flupes/digibaro2/brochure/digibaro_no-face.jpg

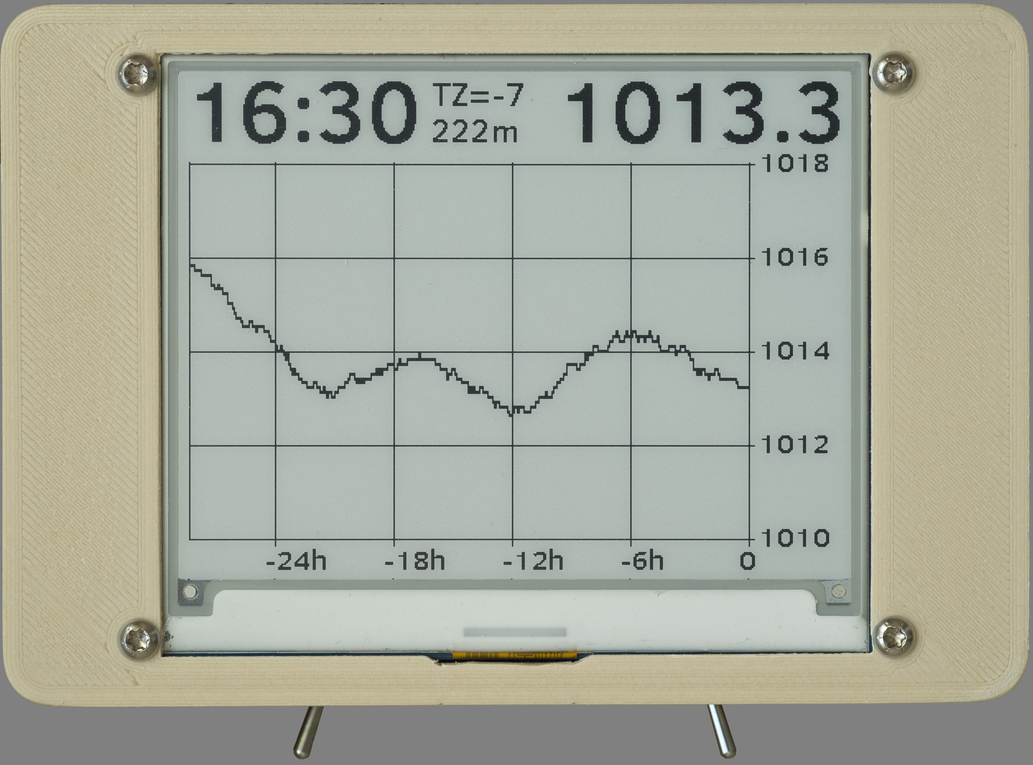
brochure/digibaro_no-face.jpg
