flupes/digibaro2/brochure/A_intro/1024px-Barograph_-_Image_from_page_45_of__Practical_physics__(1922).jpg

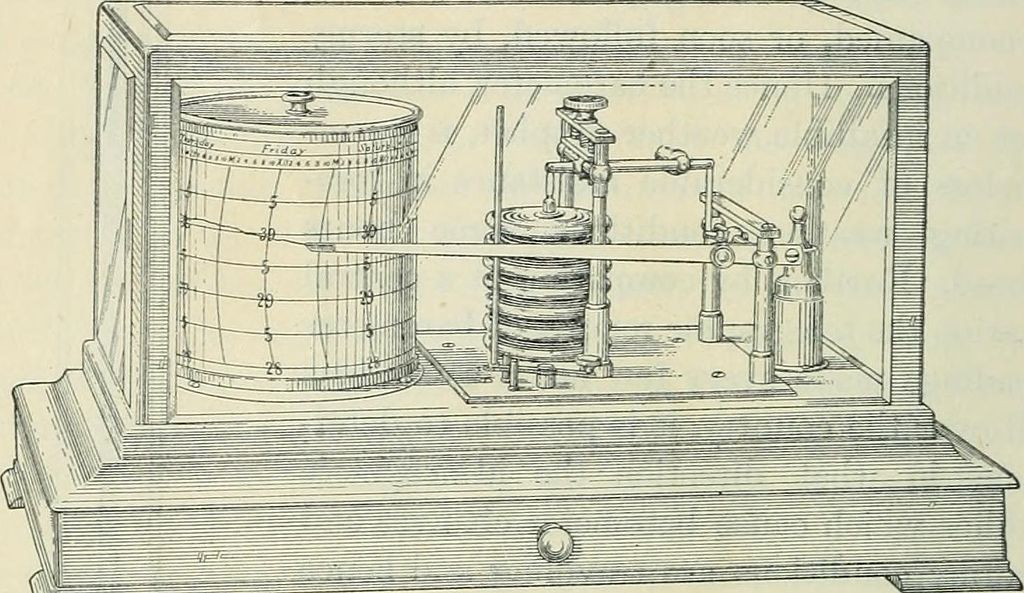
brochure/A_intro/1024px-Barograph_-_Image_from_page_45_of__Practical_physics__(1922).jpg
