flupes/digibaro2/brochure/A_intro/1926miamibarotrace.jpg

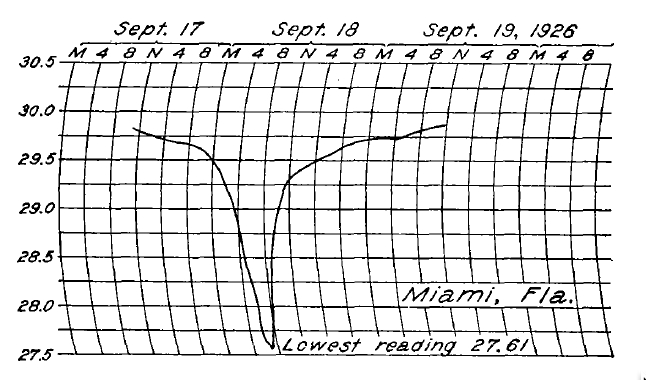
brochure/A_intro/1926miamibarotrace.jpg
