flupes/digibaro2/brochure/B_electro/B3_board-layout.png

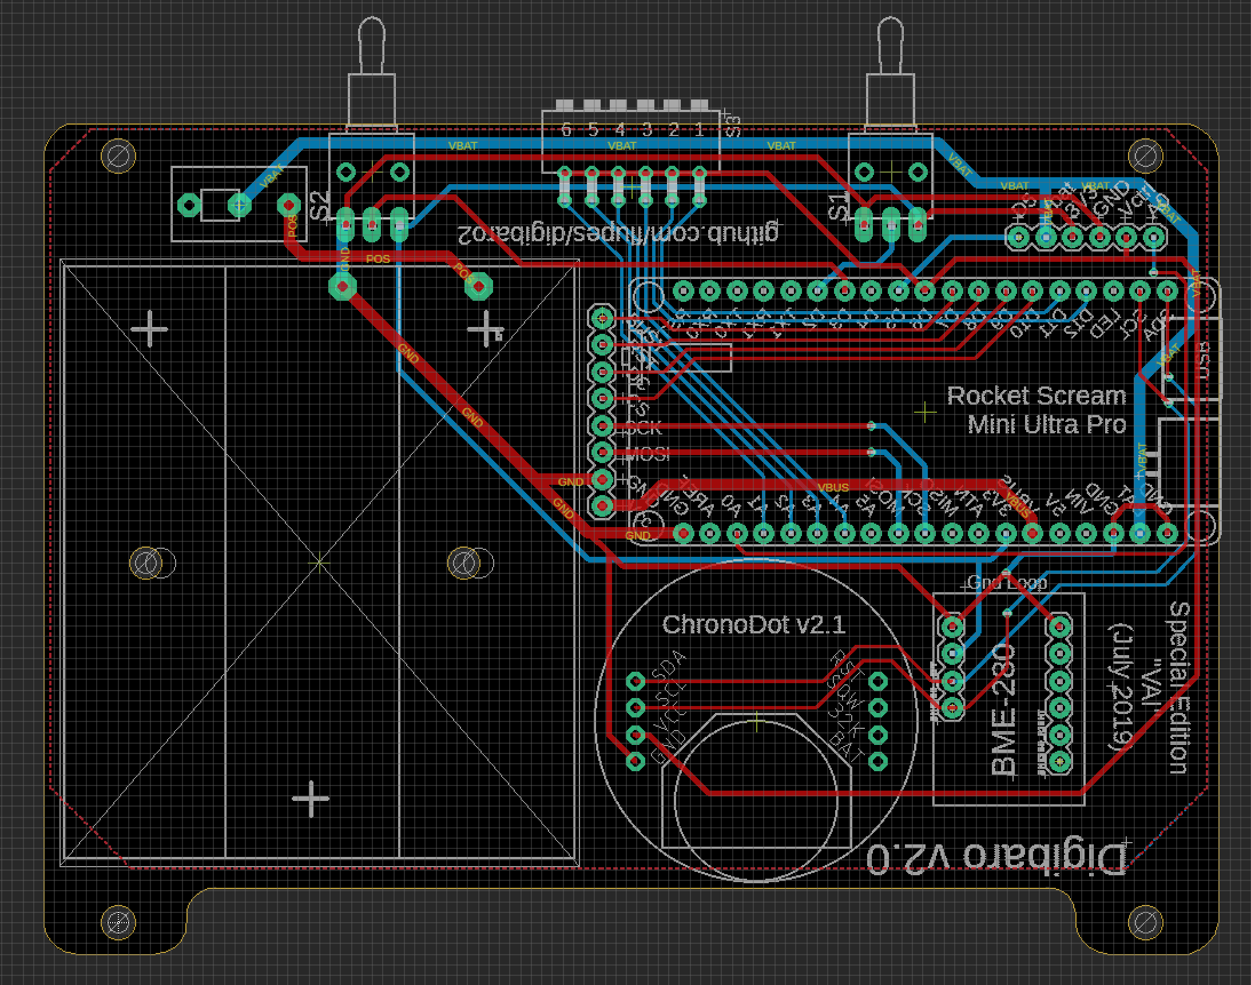
brochure/B_electro/B3_board-layout.png
