flupes/digibaro2/brochure/B_electro/B4_board-topring.png

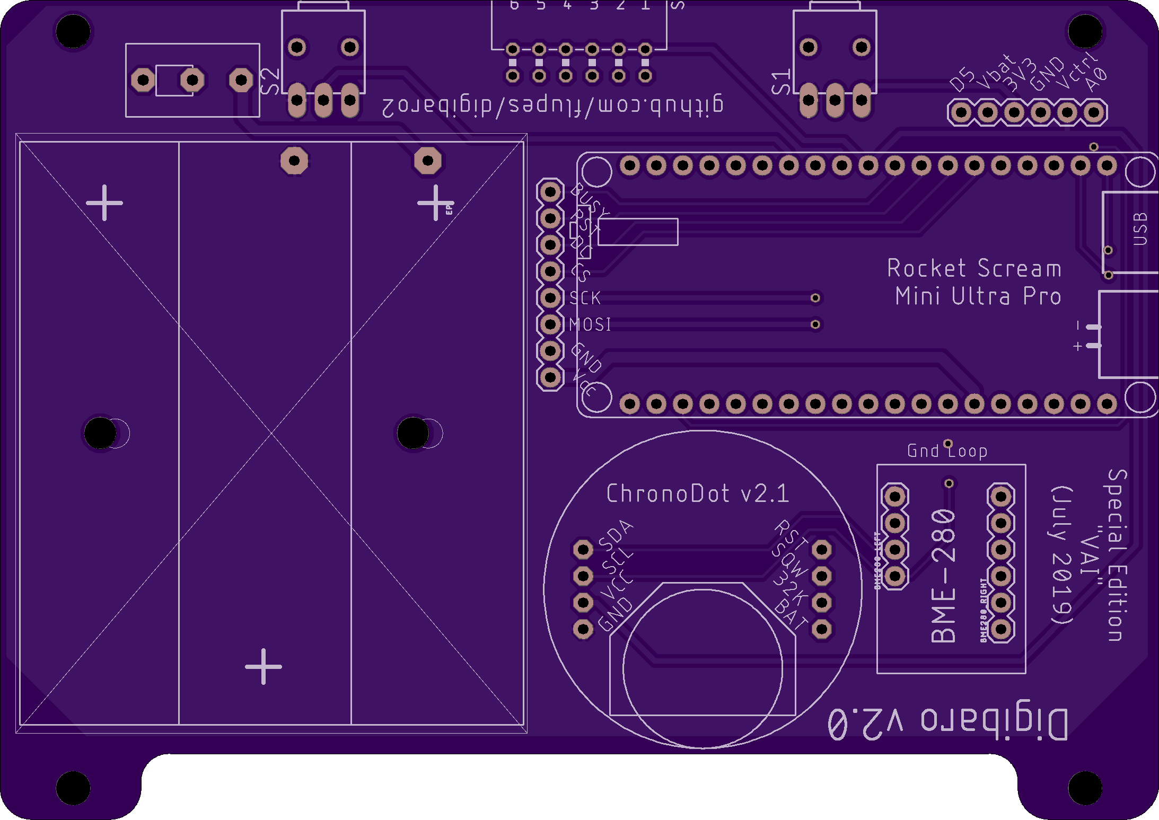
brochure/B_electro/B4_board-topring.png
