flupes/digibaro2/brochure/B_electro/B5_populated-board.jpg

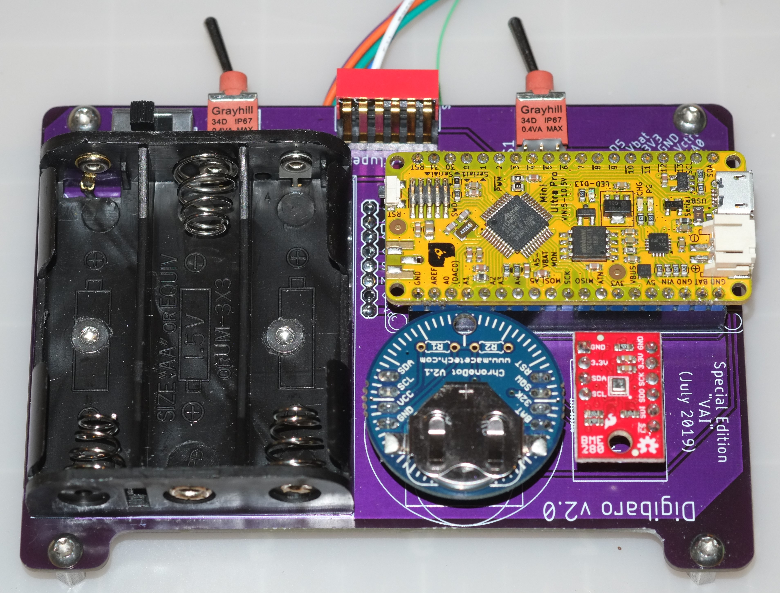
brochure/B_electro/B5_populated-board.jpg
