flupes/digibaro2/brochure/C_software/code.png

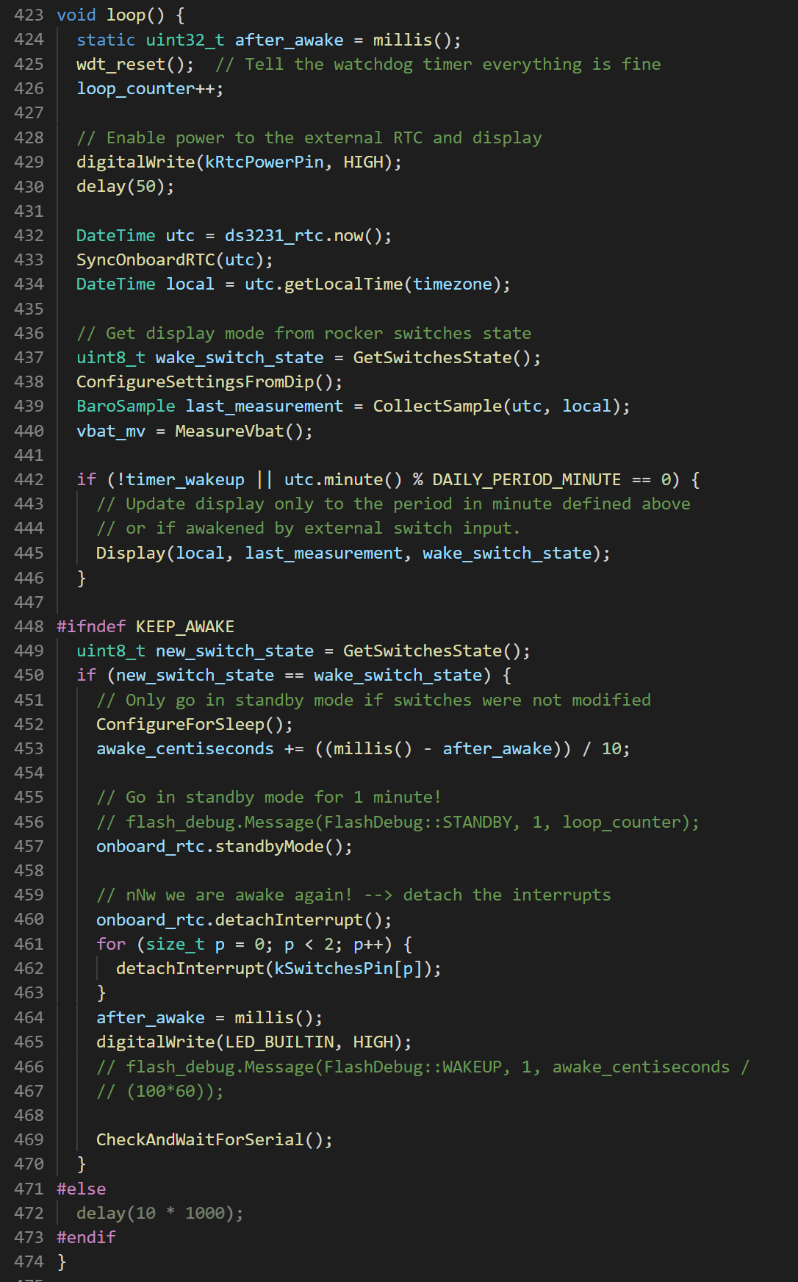
brochure/C_software/code.png
