flupes/digibaro2/brochure/digibaro_crap.jpg

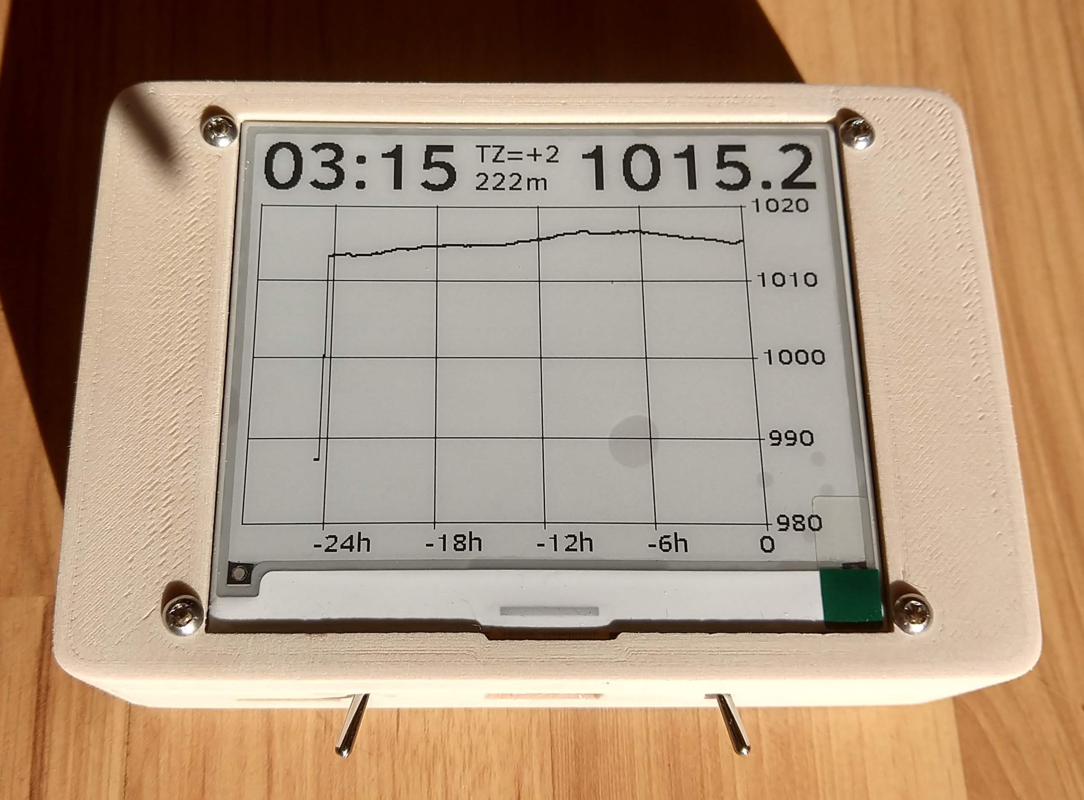
brochure/digibaro_crap.jpg
