flupes/digibaro2/brochure/digibaro_rendered.png

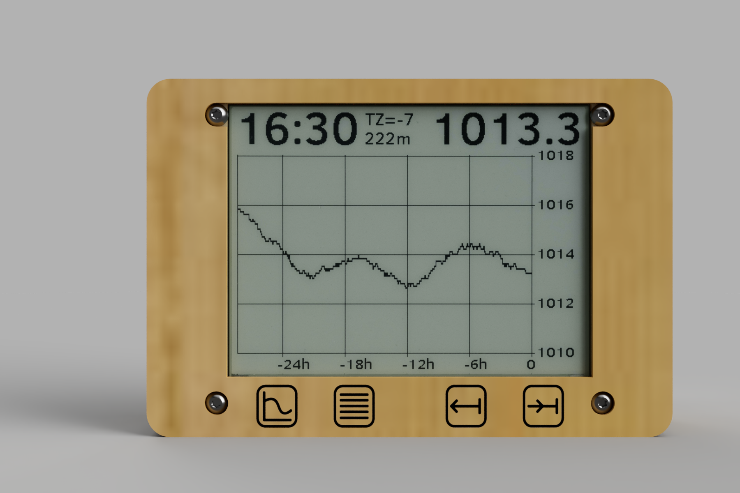
brochure/digibaro_rendered.png
