flupes/digibaro2/brochure/E_manual/dip_dst.png

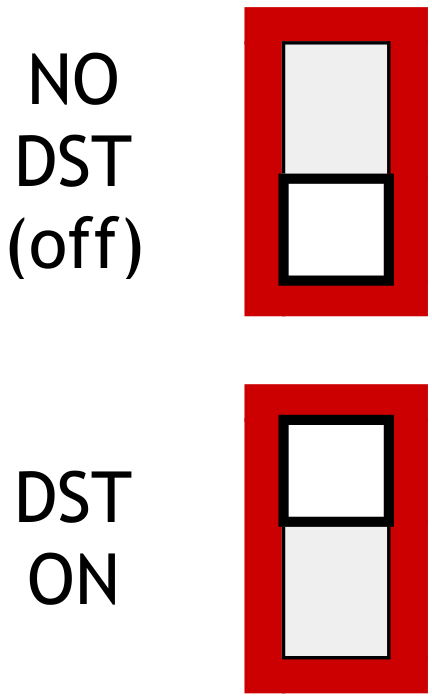
brochure/E_manual/dip_dst.png
