flupes/digibaro2/brochure/E_manual/dip_switch.png

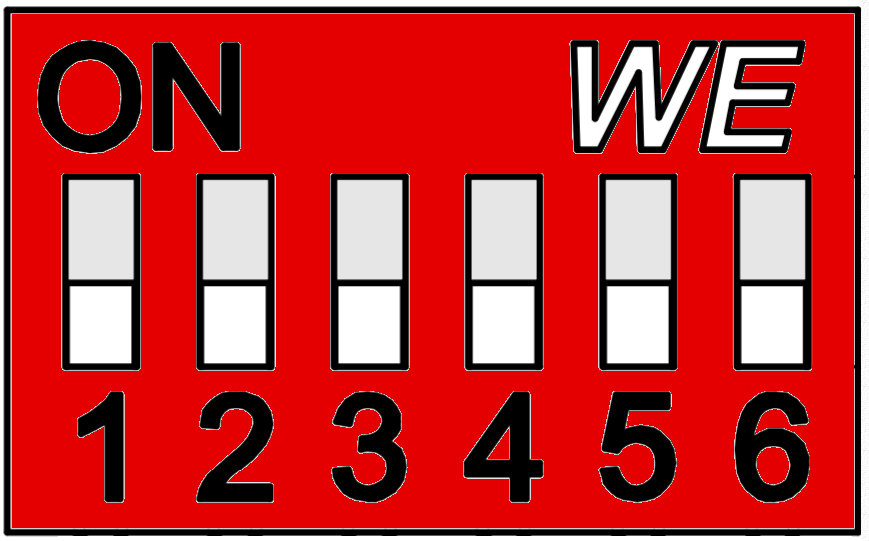
brochure/E_manual/dip_switch.png
