flupes/digibaro2/brochure/E_manual/dip_tz1.png

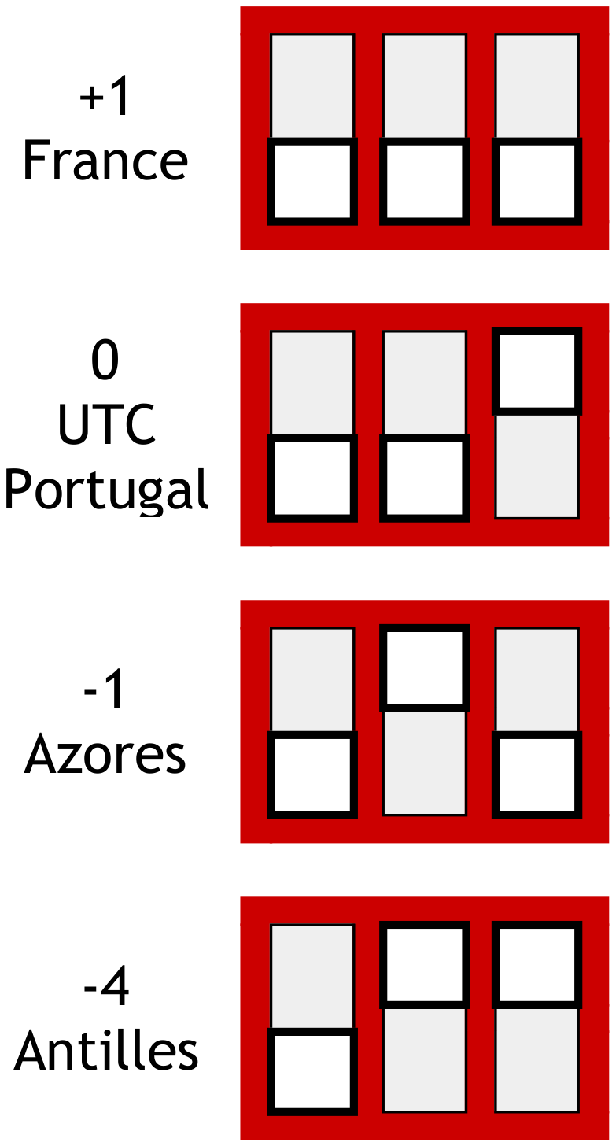
brochure/E_manual/dip_tz1.png
