flupes/digibaro2/brochure/E_manual/dip_tz2.png

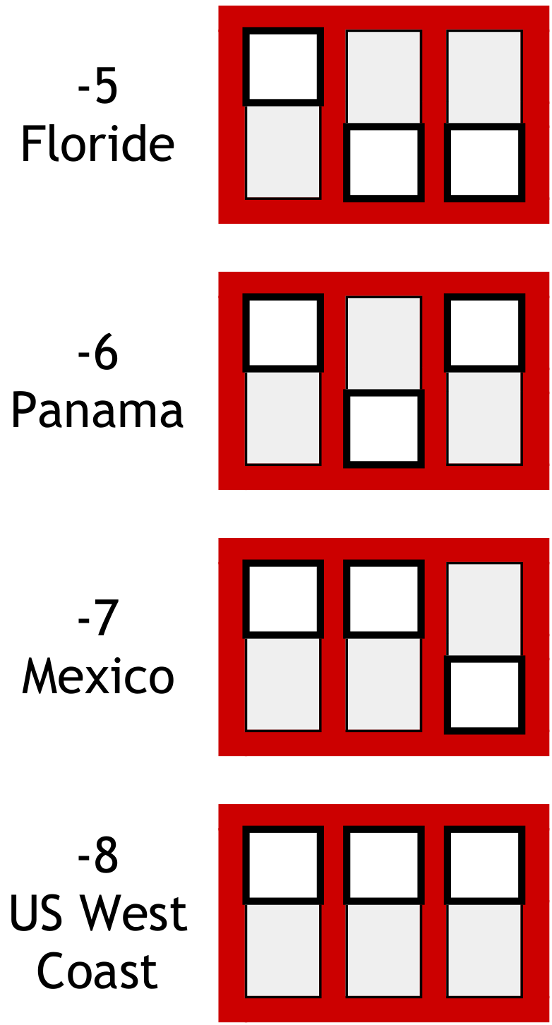
brochure/E_manual/dip_tz2.png
