flupes/digibaro2/brochure/E_manual/switch.png

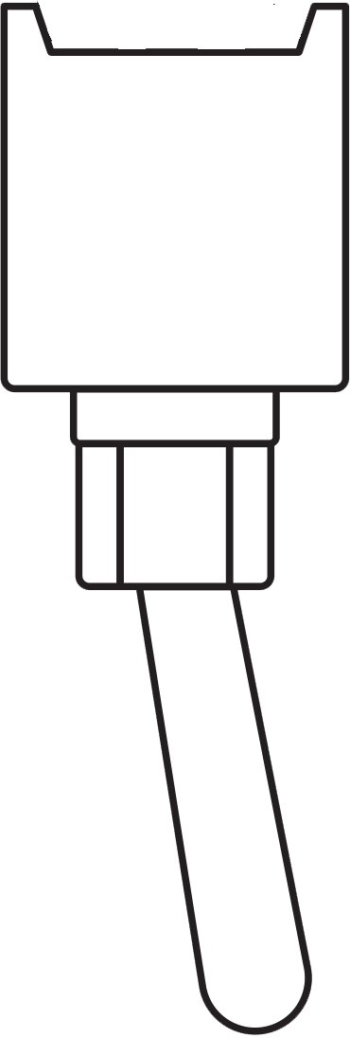
brochure/E_manual/switch.png
